HoneyOak/chopping-board/images/pcb.png

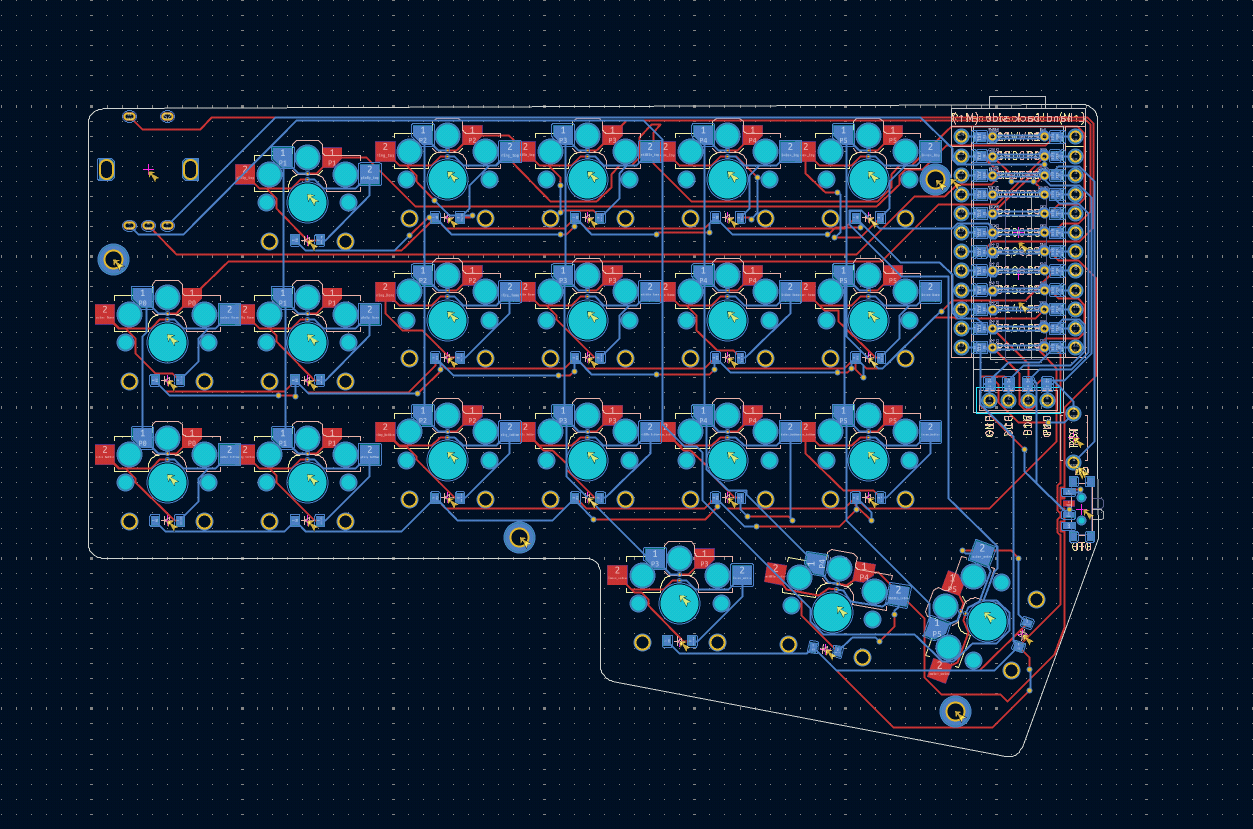
images/pcb.png
